vives-project-xp/DancingLight/Eindpresentatie/foto's/20231204_092456.jpg

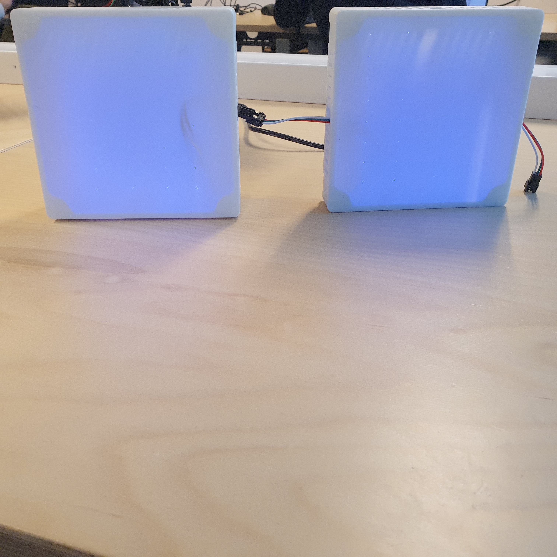
Eindpresentatie/foto's/20231204_092456.jpg
