vives-project-xp/DancingLight/Eindpresentatie/foto's/20231204_092459.jpg

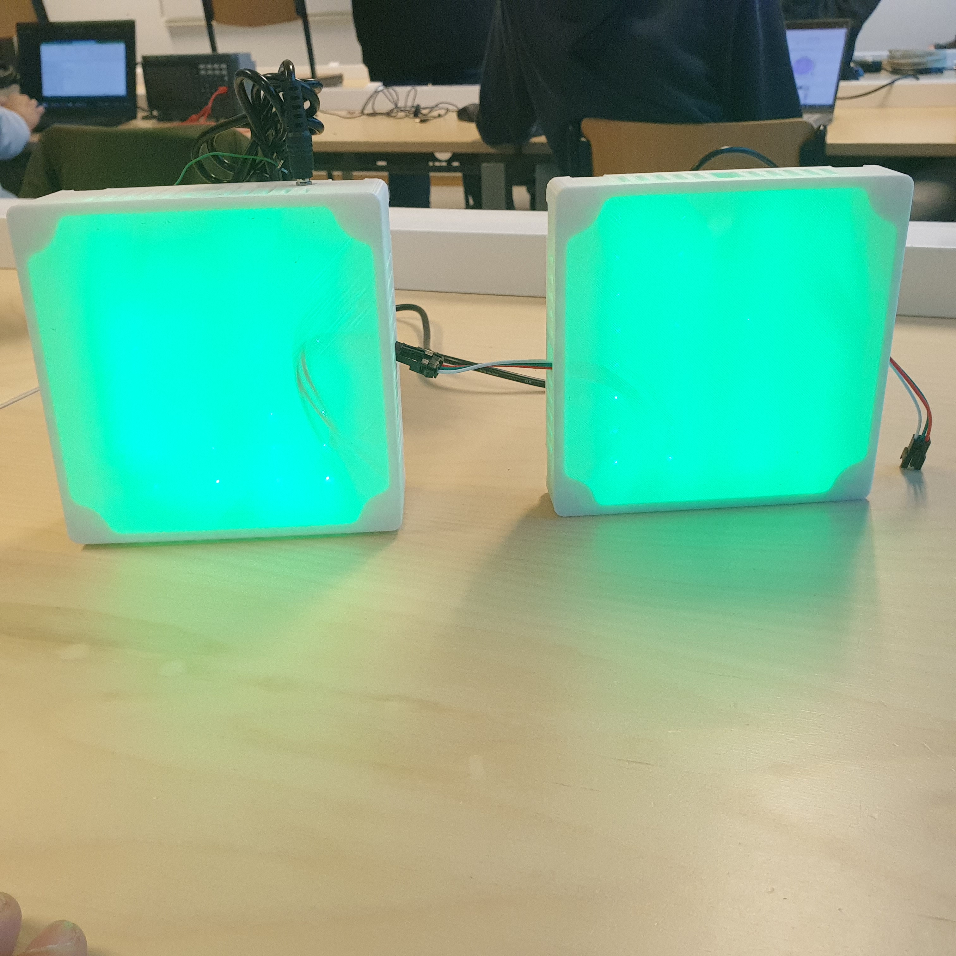
Eindpresentatie/foto's/20231204_092459.jpg
