vives-project-xp/DancingLight/Eindpresentatie/foto's/foto1.jpg

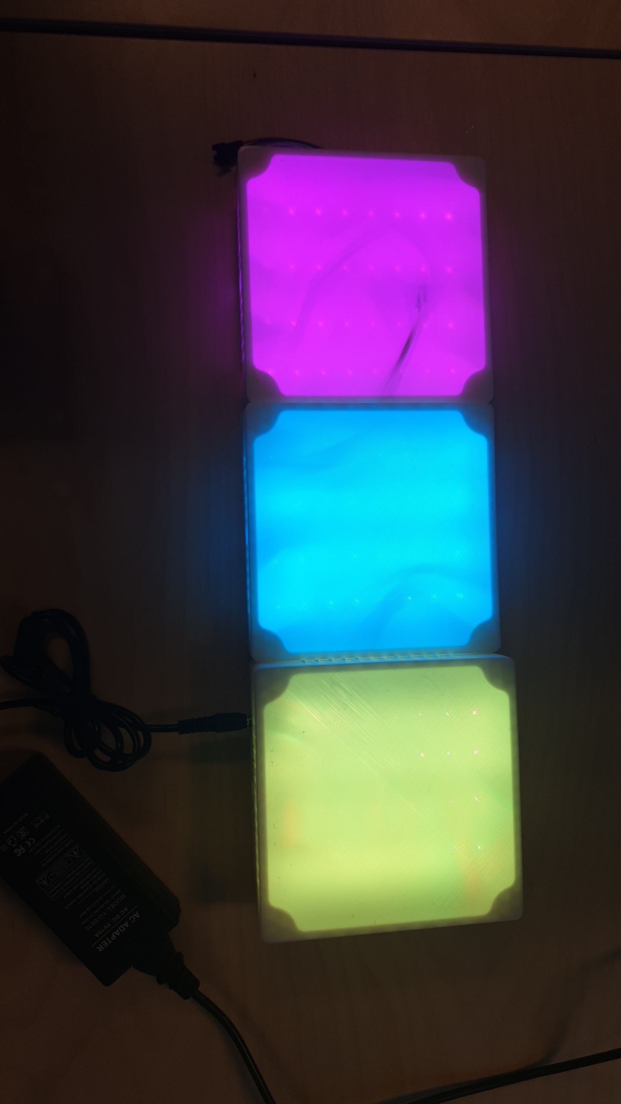
Eindpresentatie/foto's/foto1.jpg
