vives-project-xp/DancingLight/Eindpresentatie/foto's/foto2.jpg

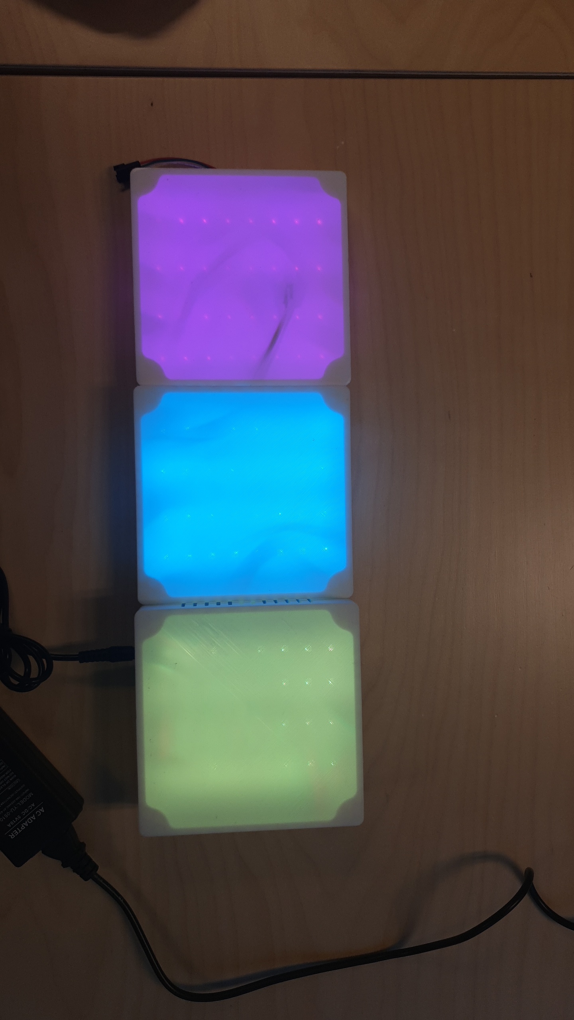
Eindpresentatie/foto's/foto2.jpg
