vives-project-xp/DancingLight/Eindpresentatie/foto's/foto3.jpg

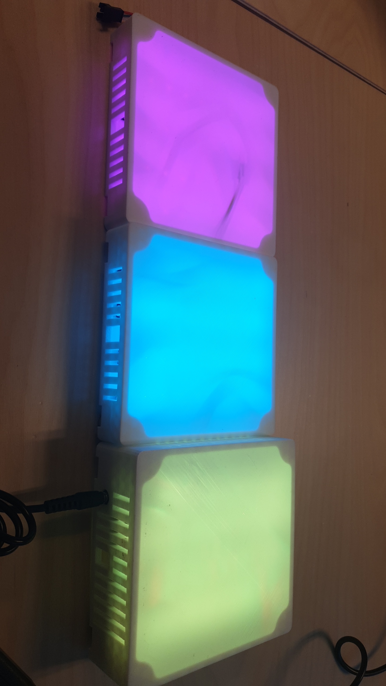
Eindpresentatie/foto's/foto3.jpg
