vives-project-xp/DancingLight/Eindpresentatie/foto's/Screenshot 2023-12-04 at 09.08.38.png

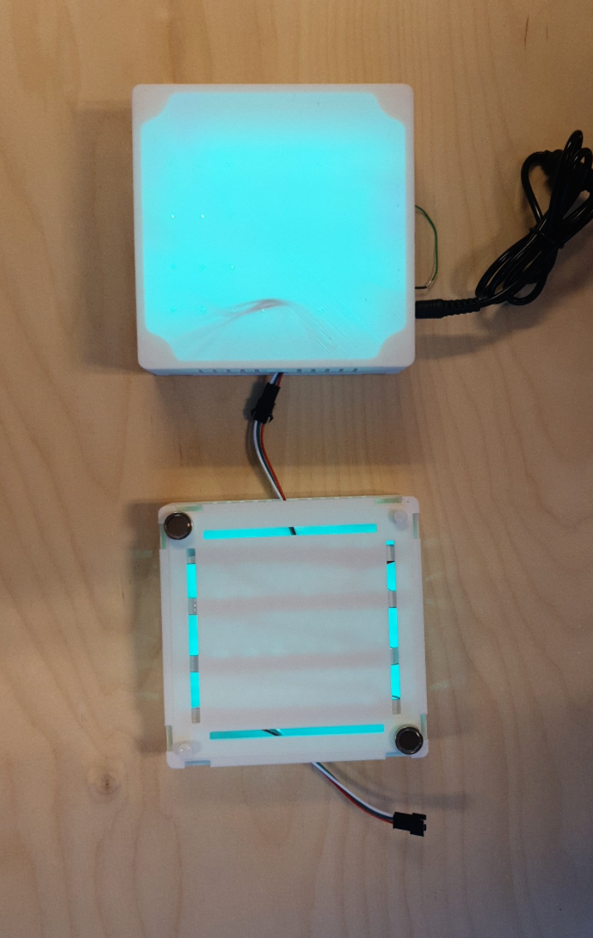
Eindpresentatie/foto's/Screenshot 2023-12-04 at 09.08.38.png
