vives-project-xp/DancingLight/Eindpresentatie/foto's/Screenshot 2023-12-04 at 09.09.58.png

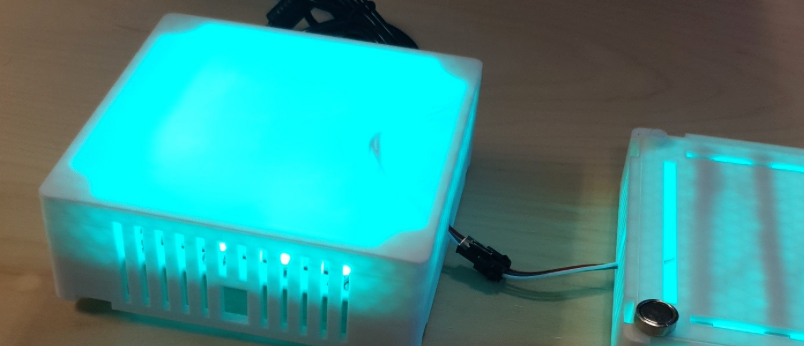
Eindpresentatie/foto's/Screenshot 2023-12-04 at 09.09.58.png
