vives-project-xp/DancingLight/Eindpresentatie/foto's/Screenshot 2023-12-04 at 10.01.44.png

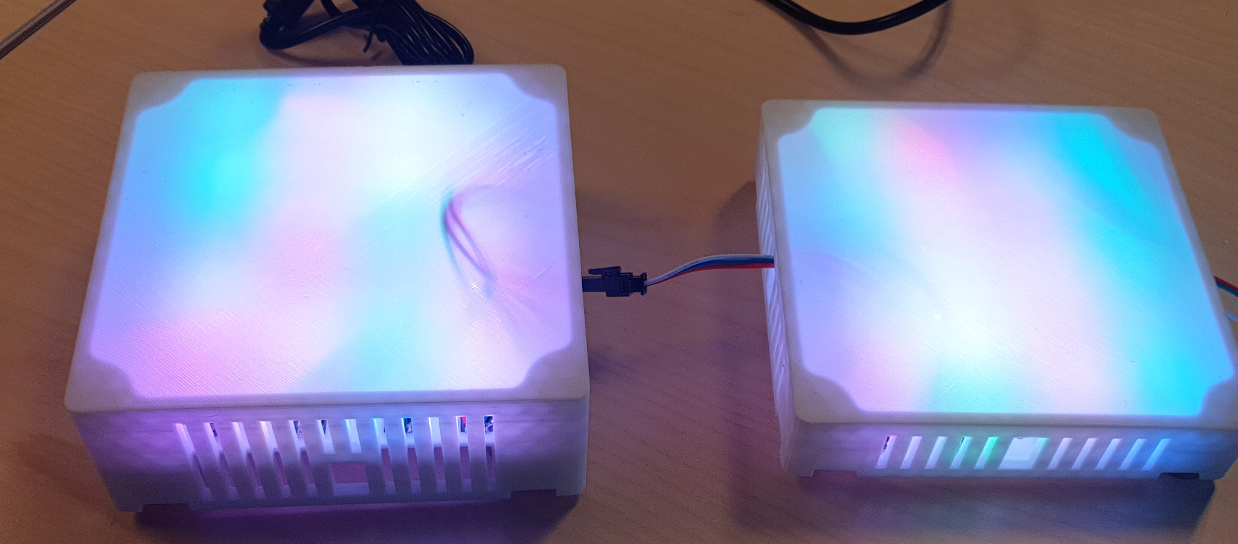
Eindpresentatie/foto's/Screenshot 2023-12-04 at 10.01.44.png
