vives-project-xp/DancingLight/Images/Case.png

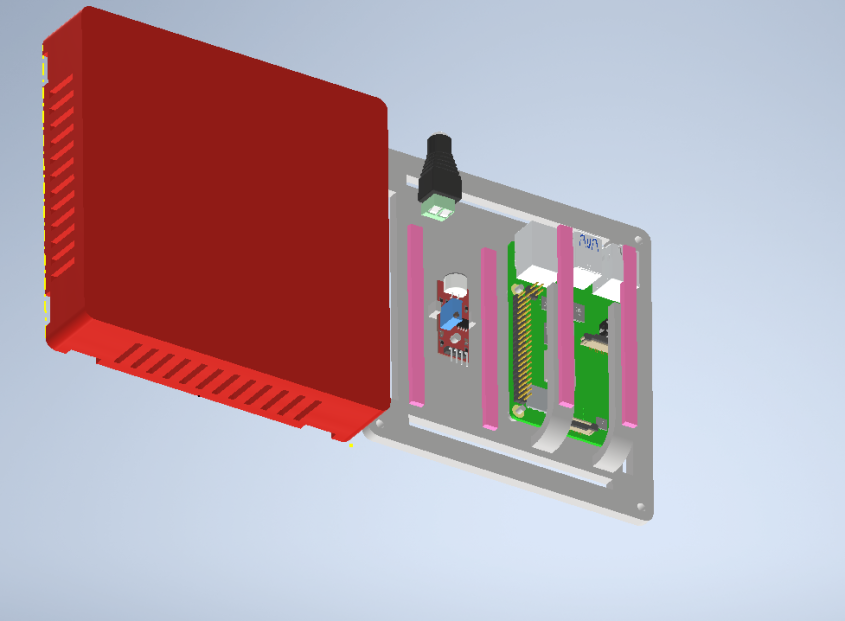
Images/Case.png
