vives-project-xp/DancingLight/Images/Presentatie/20231211_090015.jpg

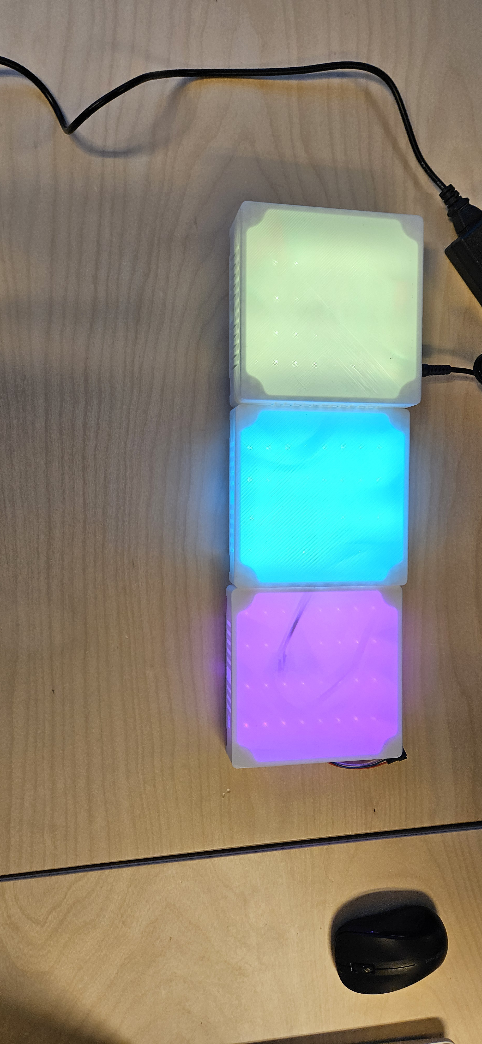
Images/Presentatie/20231211_090015.jpg
