vives-project-xp/DancingLight/Tekeningen/3D stl tekeningen/STL 16-10-2023 niet meer nodig/overzicht-3D-opstelling.JPG

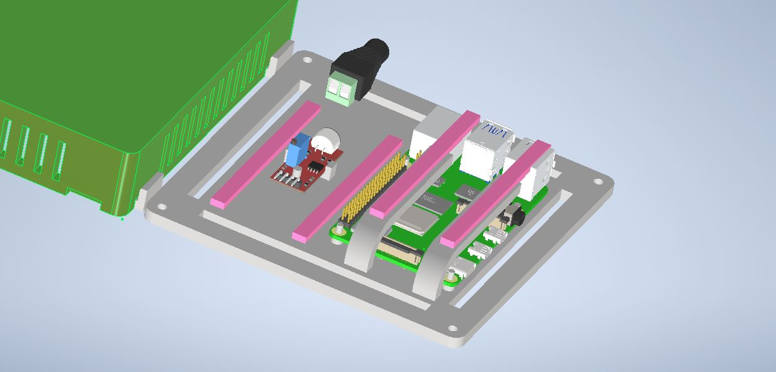
Tekeningen/3D stl tekeningen/STL 16-10-2023 niet meer nodig/overzicht-3D-opstelling.JPG
