vives-project-xp/DancingLight/Tekeningen/13_11_2023 stukken niet meer nodig/dc-barrel-jack-adapter-female-with-screw-terminals-1.snapshot.2/DC_Barrel_Jack_Adapter_Female.PNG

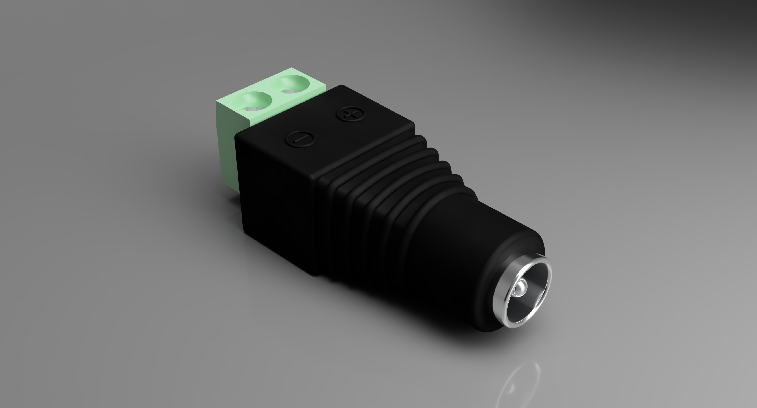
Tekeningen/13_11_2023 stukken niet meer nodig/dc-barrel-jack-adapter-female-with-screw-terminals-1.snapshot.2/DC_Barrel_Jack_Adapter_Female.PNG
