vives-project-xp/DancingLight/Tekeningen/13_11_2023 stukken niet meer nodig/raspberrypi/Microphone Plug, RPi4ModelB.SLDPRT

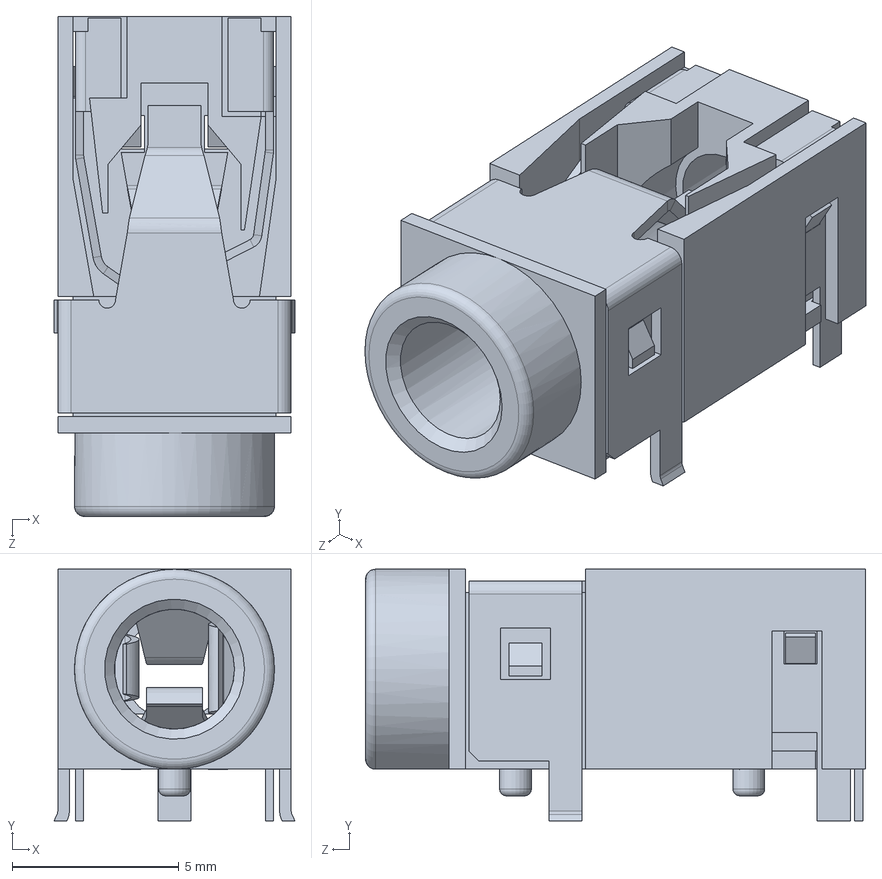
[picture p50: CAD file, 2023-11-12]
Tekeningen/13_11_2023 stukken niet meer nodig/raspberrypi/Microphone Plug, RPi4ModelB.SLDPRT
7.23 x 7.55 x 15.0 mm
