vives-project-xp/DancingLight/Tekeningen/3D stl tekeningen/STL 14-11-2023/spacer dubbele hoogte behuizing zonder magneet.stl

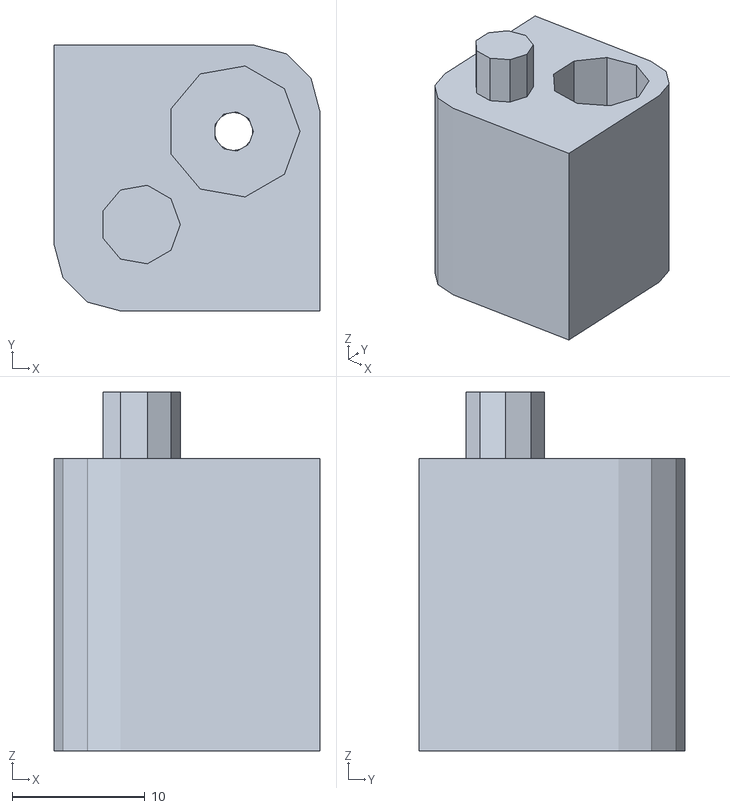
[picture p51: CAD file, 2023-11-20]
Tekeningen/3D stl tekeningen/STL 14-11-2023/spacer dubbele hoogte behuizing zonder magneet.stl
20.0 x 20.0 x 27.0
