vives-project-xp/DancingLight/Tekeningen/3D stl tekeningen/STL 16-10-2023 niet meer nodig/Koppelstuk.stl

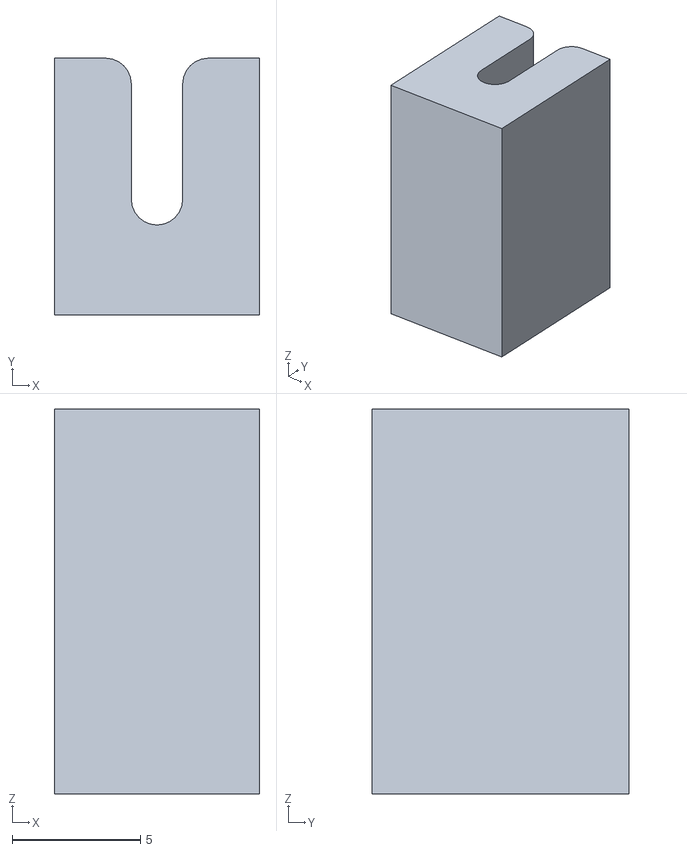
[picture p52: CAD file, 2023-10-16]
Tekeningen/3D stl tekeningen/STL 16-10-2023 niet meer nodig/Koppelstuk.stl
8.00 x 10.0 x 15.0
