vives-project-xp/DancingLight/Tekeningen/3D stl tekeningen/STL 14-11-2023/Led deksel hub zonder pi.stl

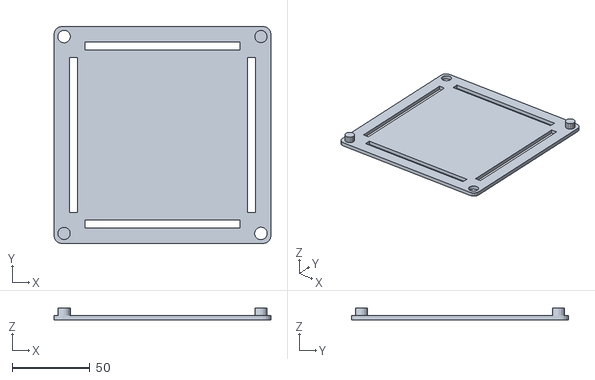
[picture p53: CAD file, 2023-11-20]
Tekeningen/3D stl tekeningen/STL 14-11-2023/Led deksel hub zonder pi.stl
140.0 x 140.0 x 8.00
