vives-project-xp/DancingLight/Tekeningen/13_11_2023 stukken niet meer nodig/raspberrypi/Female Micro HDMI Connector, RPi4ModelB.SLDPRT

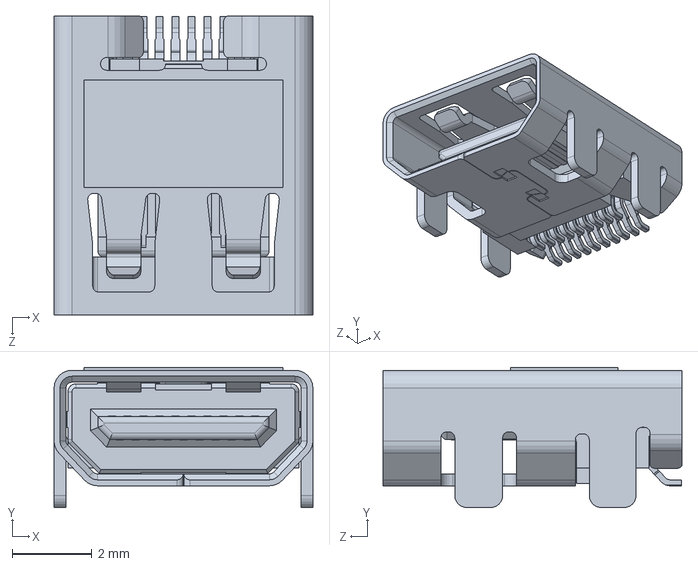
[picture p54: CAD file, 2023-11-12]
Tekeningen/13_11_2023 stukken niet meer nodig/raspberrypi/Female Micro HDMI Connector, RPi4ModelB.SLDPRT
6.50 x 3.52 x 7.50 mm
