vives-project-xp/DancingLight/Tekeningen/13_11_2023 stukken niet meer nodig/raspberrypi/VIA VL805 PCIe USB 3.0 controller, RPi4ModelB.SLDPRT

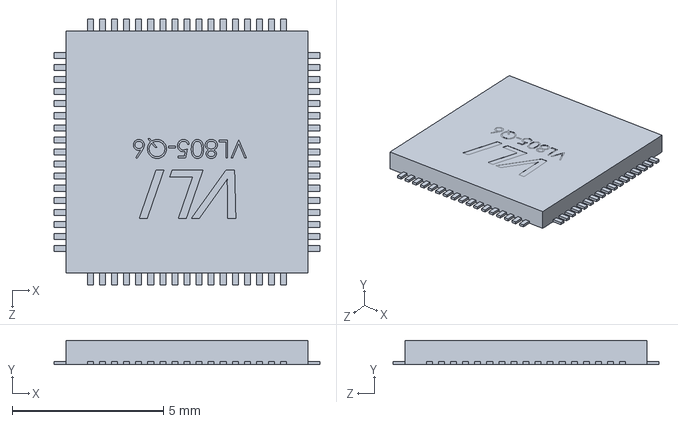
[picture p55: CAD file, 2023-11-12]
Tekeningen/13_11_2023 stukken niet meer nodig/raspberrypi/VIA VL805 PCIe USB 3.0 controller, RPi4ModelB.SLDPRT
8.80 x 0.8 x 8.80 mm
