vives-project-xp/DancingLight/Tekeningen/13_11_2023 stukken niet meer nodig/raspberrypi/Cypress CYW43455 Wireless Module Cover, RPi4ModelB.SLDPRT

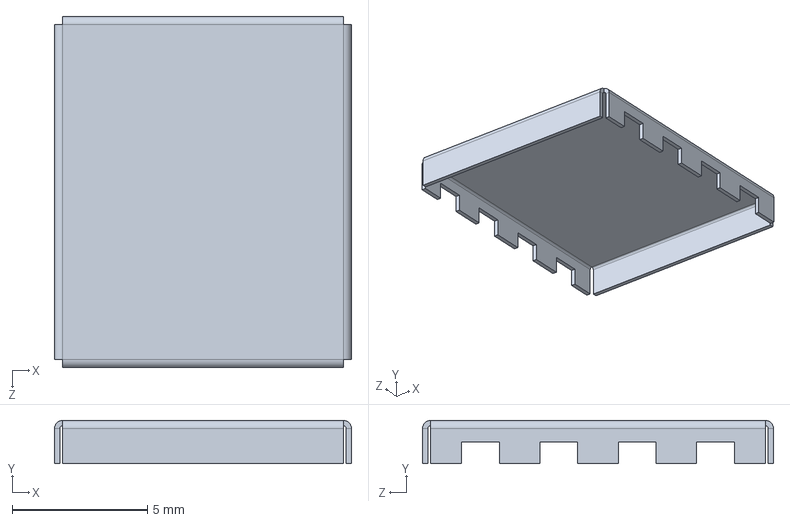
[picture p56: CAD file, 2023-11-12]
Tekeningen/13_11_2023 stukken niet meer nodig/raspberrypi/Cypress CYW43455 Wireless Module Cover, RPi4ModelB.SLDPRT
11.0 x 1.60 x 13.0 mm
