vives-project-xp/DancingLight/Tekeningen/13_11_2023 stukken niet meer nodig/raspberrypi/2.54 mm DUPONT MALE PIN HEADER, POE, 2X2, RPi4ModelB.SLDPRT

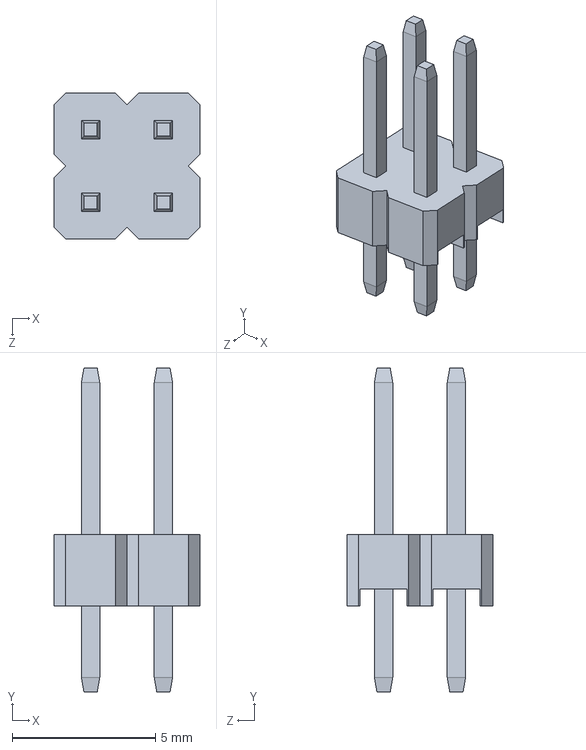
[picture p57: CAD file, 2023-11-12]
Tekeningen/13_11_2023 stukken niet meer nodig/raspberrypi/2.54 mm DUPONT MALE PIN HEADER, POE, 2X2, RPi4ModelB.SLDPRT
5.08 x 11.3 x 5.08 mm
